Ese-G-Oduware/buck-converter-LTSpice-/schematic/BUCK_CONVERTER.asc

C1: cap; 10µ
CBOOT: cap; 100nF
D1: diode; MBR745
DBOOT: diode
L1: ind; 100µ; Rser=1m
LOAD: res; 5
NMOS: nmos; BSC010NE2LS
PULSE: voltage; PULSE(0 5 0 10n 10n 4.17u 10u)
RBOOT: res; 2.2
U1: LTC4440
V1: voltage; 12
Named nets: 0, Vin, IND-DIO
.tran 0 2m 0 20ns
.meas tran my_vpp PP V(n001) from=1.8m to=2m
